edilsoncorrea/anet_a8_150x150/stl/Suporte_Placa_Ramps_v6.stl

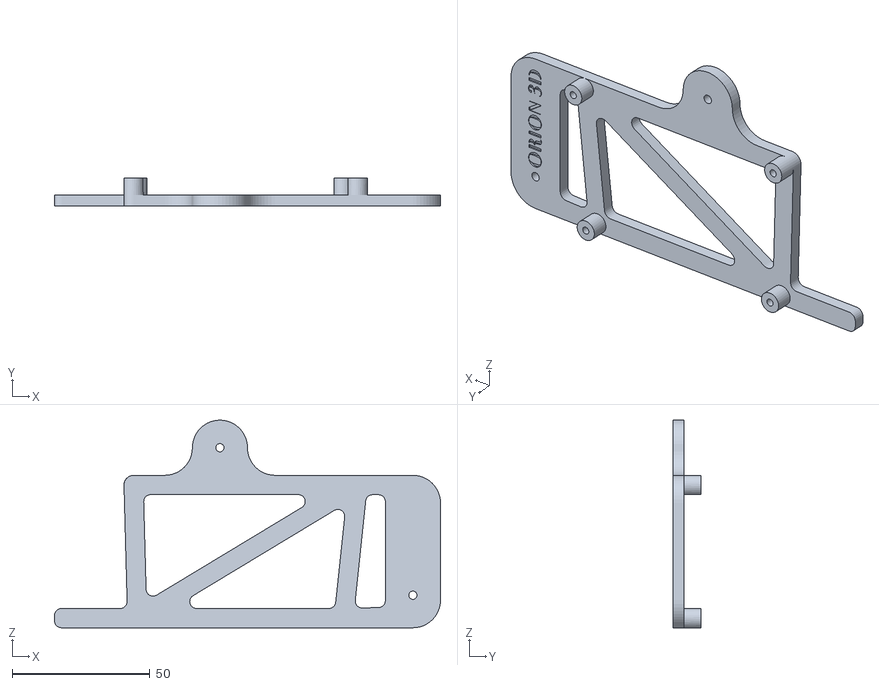
[picture p16: CAD file, 2023-06-11]
stl/Suporte_Placa_Ramps_v6.stl
140.0 x 10.0 x 75.3
