edilsoncorrea/anet_a8_150x150/stl/Tensionador_da_Correia_Y_-_Base_v6.stl

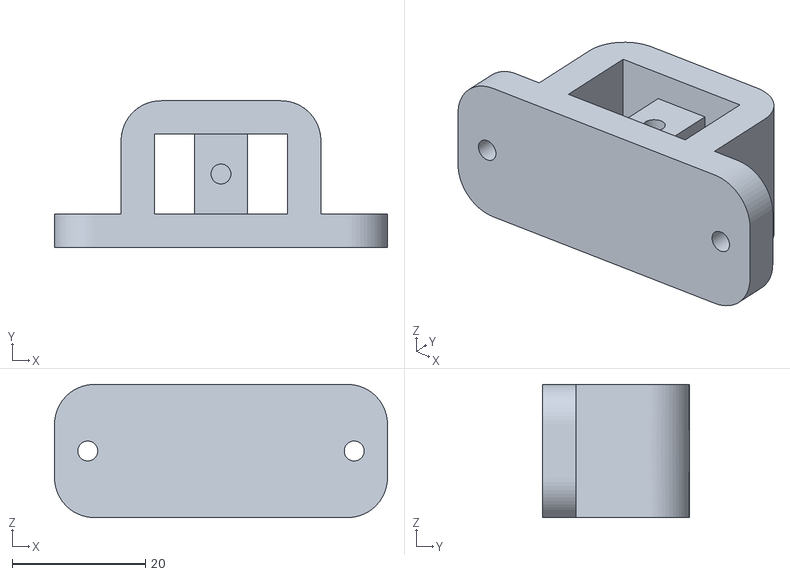
[picture p17: CAD file, 2023-06-11]
stl/Tensionador_da_Correia_Y_-_Base_v6.stl
50.0 x 22.0 x 20.0
