edilsoncorrea/anet_a8_150x150/stl/Suporte_Conector_Tomada_v4.stl

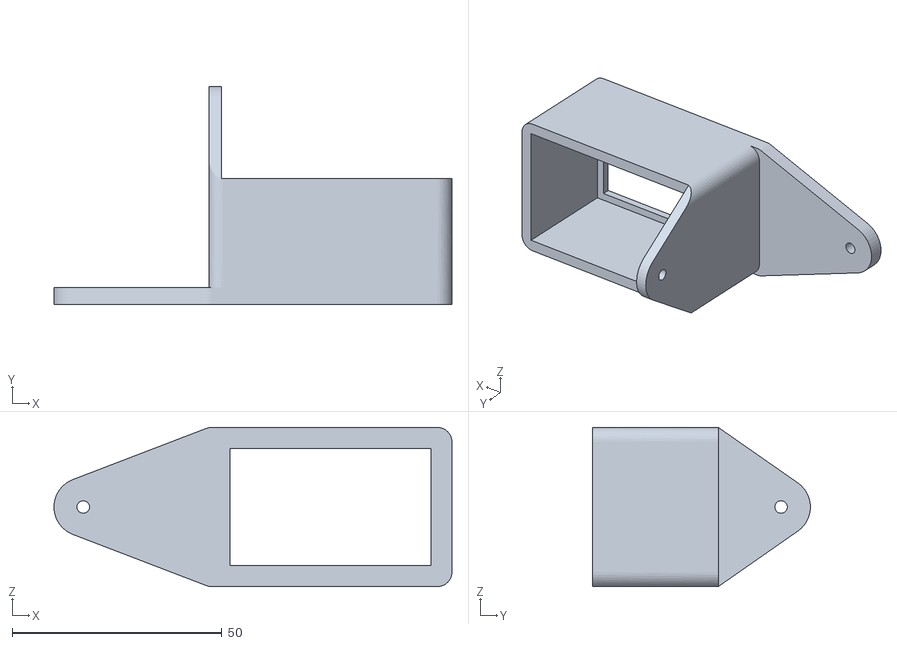
[picture p18: CAD file, 2023-06-11]
stl/Suporte_Conector_Tomada_v4.stl
95.0 x 52.0 x 38.0
